dngvmnh/Trash_Collecting_Robot/PII/BottleDetection/Past-versions/calibrate/images/image0.jpg

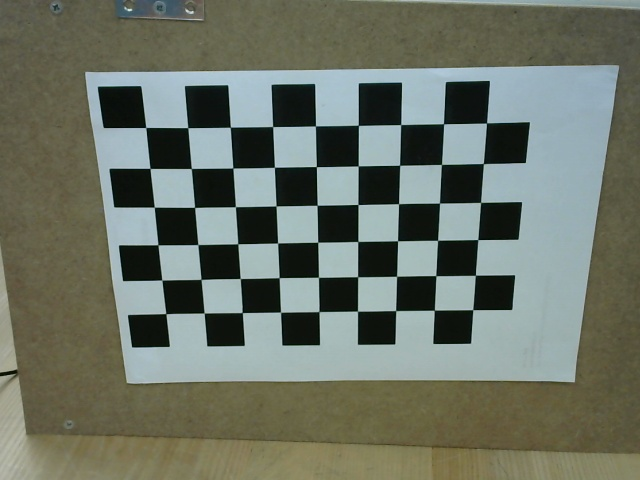
PII/BottleDetection/Past-versions/calibrate/images/image0.jpg
