dngvmnh/Trash_Collecting_Robot/PII/BottleDetection/Past-versions/calibrate/images/image1.jpg

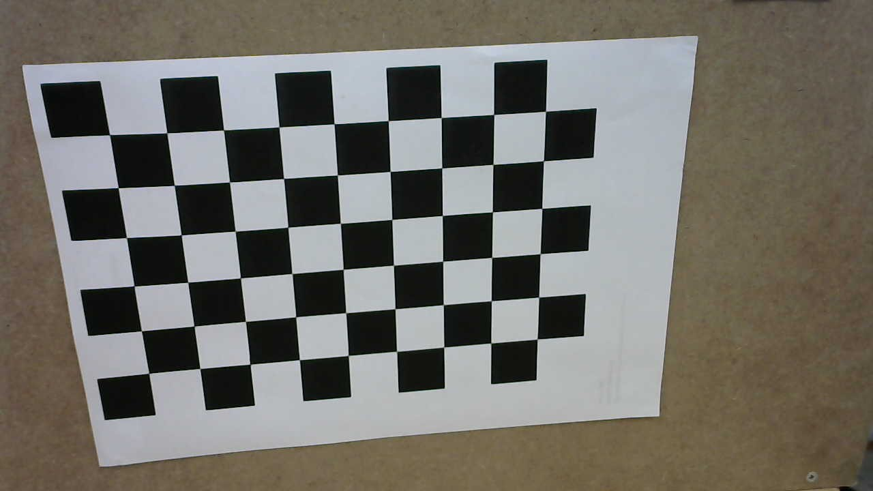
PII/BottleDetection/Past-versions/calibrate/images/image1.jpg
