dngvmnh/Trash_Collecting_Robot/PII/BottleDetection/Past-versions/flippedBottle.py

from imageai.Detection import ObjectDetection
import os
import cv2
import math
execution_path = os.getcwd()
cam = cv2.VideoCapture(0)
if not cam.isOpened():
    print('cam is not opening')
    exit()
cnt = -1
def info(frame,object):
    endX = frame.shape[1]
    midY = int(frame.shape[0]//2)
    difY = midY - (object["box_points"][1] + object["box_points"][3])//2
    difX = endX - (object["box_points"][0] + object["box_points"][2])//2
    dX = endX - max(object["box_points"][0],object["box_points"][2])
    distanceX = (142.902*(math.e**(2.512*(dX/endX)))-132.985+400)
    if difX == 0:
        absAngle = 0
    else: 
        absAngle = math.atan(difY/difX)
    distance = distanceX/math.cos(absAngle)
    return int(math.degrees(absAngle)), int(distance)
def detect(frame):
    detections =  detector.detectObjectsFromImage(input_image=frame,
                                                    minimum_percentage_probability=80,
                                                    display_percentage_probability = True,
                                                    display_object_name = True)
    for eachObject in detections:
        if eachObject['name']=='bottle':
            return eachObject
        
def center():
    adjust = True
    frc = 0
    while (adjust == True):
        frc += 1
        if (frc%30 == 0):
            ret, frame = cam.read()
            frame = cv2.rotate(frame, cv2.ROTATE_90_CLOCKWISE)
            object = detect(frame)
            if (object):
                cv2.imshow('frame', frame)
                angle = info(frame,object)[0]
                print('Current angle: ' + str(angle))
                if (abs(angle) <= 10):
                    print('centered')
                    adjust = False
                elif (angle < -45):
                    print('far right')
                elif (angle < 0):
                    print('near right')
                elif (angle < 45):
                    print('near left')
                else:
                    print('far left')
            else:
                print('Object out of frame')
    print ('Bottle {} mm away, centered'.format(info(frame,object)[1], info(frame,object)[0]))
    print("--------------------------------")
detector = ObjectDetection()
detector.setModelTypeAsYOLOv3()
detector.setModelPath(os.path.join(execution_path, "OpenCV_Robot/PII_Robot/BottleDetection/models/yolov3.pt"))
detector.loadModel()

while True:
    cnt += 1
    ret, frame = cam.read()
    frame = cv2.rotate(frame, cv2.ROTATE_90_CLOCKWISE)
    if (cnt%60==0):
        object = detect(frame)
        if object:
            print('Bottle detected with probability: {}%'.format(object["percentage_probability"]))
            print('Bottle {} mm away at an angle of {} degrees'.format(info(frame,object)[1], info(frame,object)[0]))
            center()
        else:
            print('No bottle found')
    if not ret:
        break
    cv2.imshow('frame', cv2.rotate(frame, cv2.ROTATE_90_COUNTERCLOCKWISE))
    if cv2.waitKey(1)==ord('q'):
        break
cam.release()
cv2.destroyAllWindows()
